codekitchen/drawbot/models/scad_libs/hulls.scad

module sequentialHull(){
    for (i = [0:$children-2])
        hull(){
            children(i);
            children(i+1);
        }
}
